merocle/mincab/MinCab_v3.0/Renders/1.png

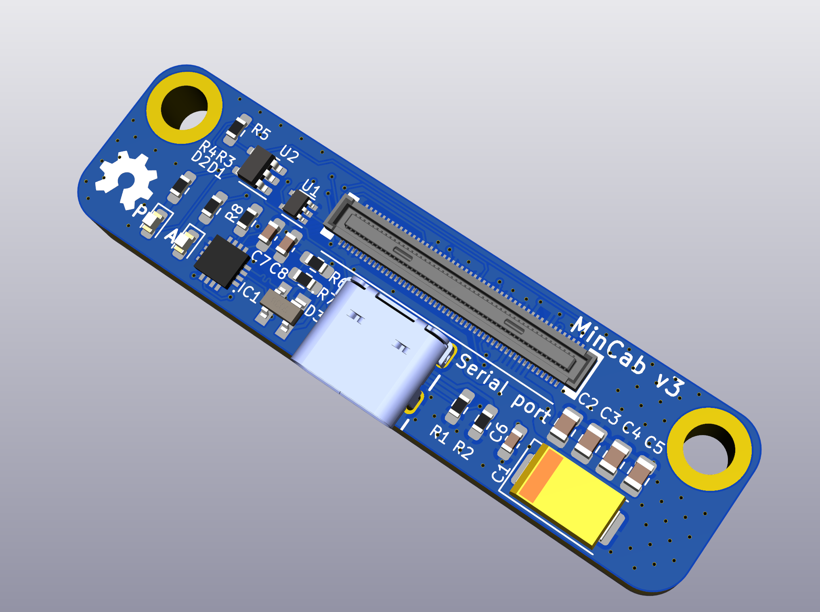
MinCab_v3.0/Renders/1.png
