merocle/mincab/MinCab_v3.0/Renders/2.png

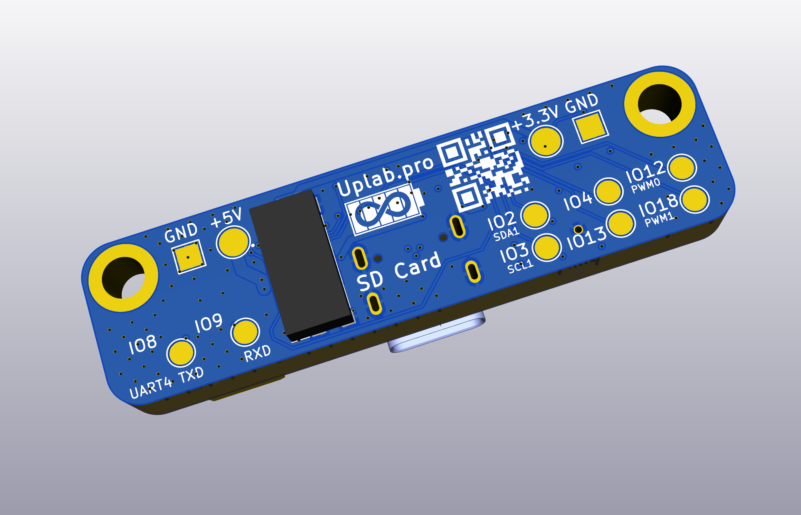
MinCab_v3.0/Renders/2.png
