merocle/mincab/Photos/1.jpg

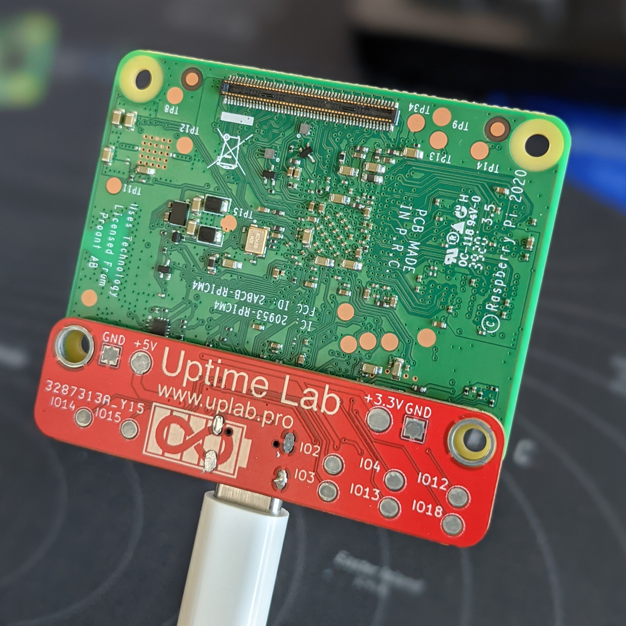
Photos/1.jpg
