merocle/mincab/Photos/2.jpg

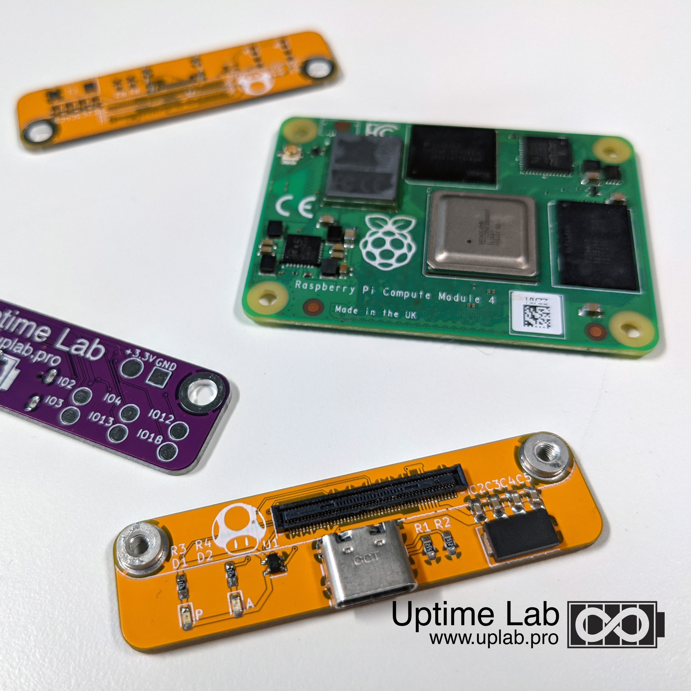
Photos/2.jpg
