merocle/mincab/Photos/3.jpg

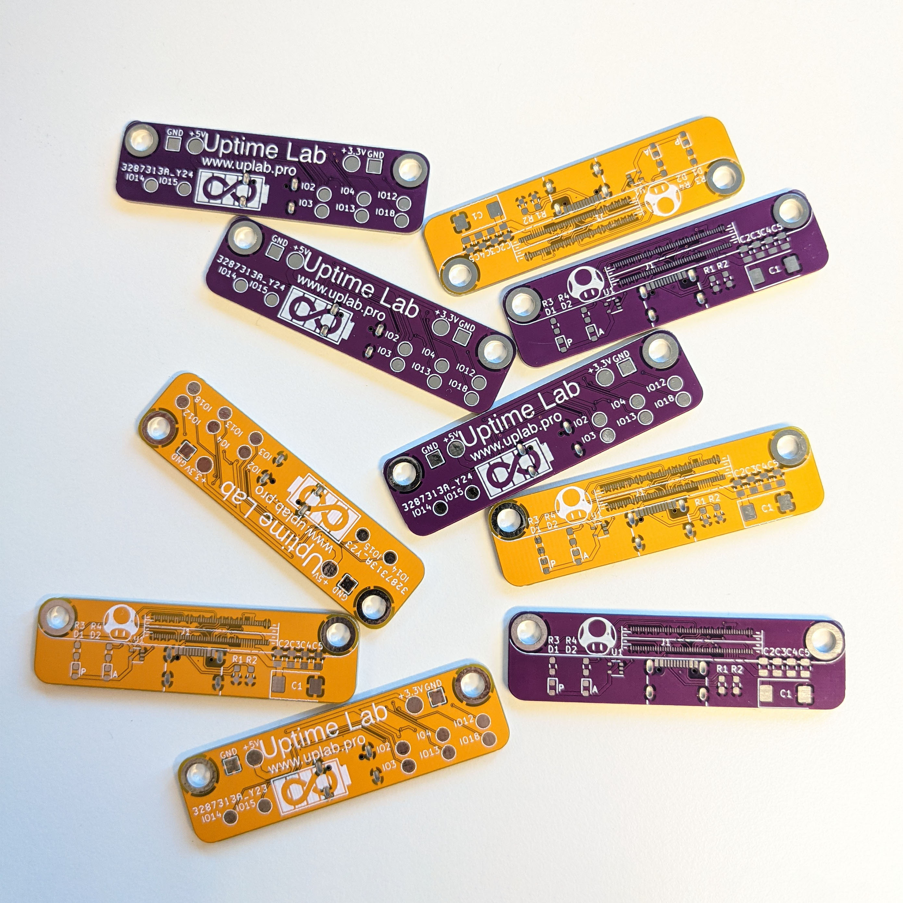
Photos/3.jpg
