merocle/mincab/Photos/4.jpg

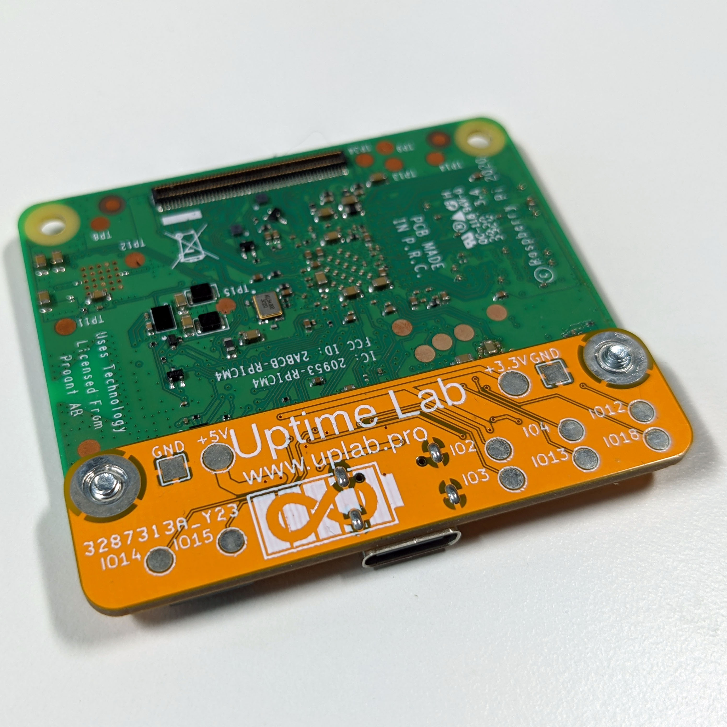
Photos/4.jpg
