merocle/mincab/Photos/5.jpg

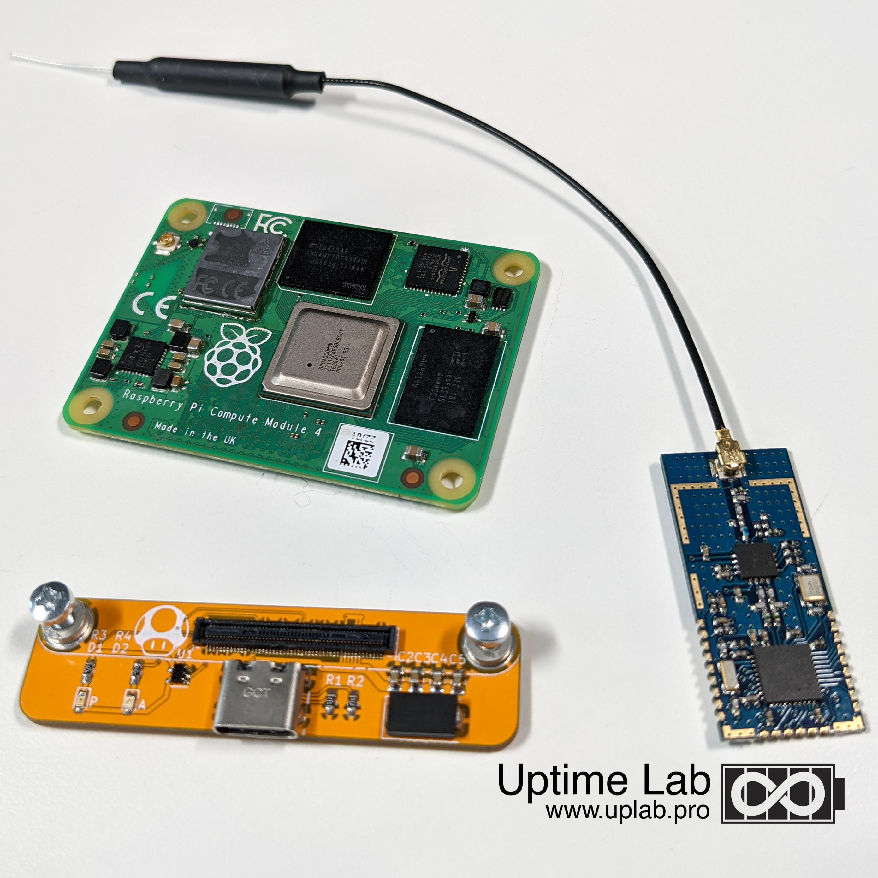
Photos/5.jpg
