merocle/mincab/Photos/6.jpg

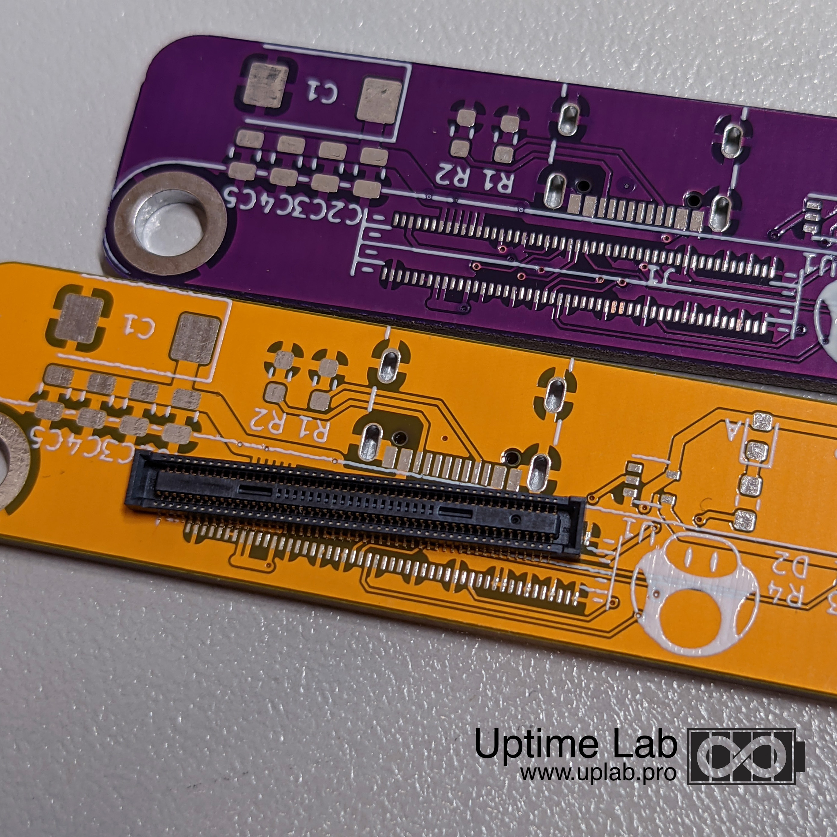
Photos/6.jpg
