merocle/mincab/Photos/7.jpg

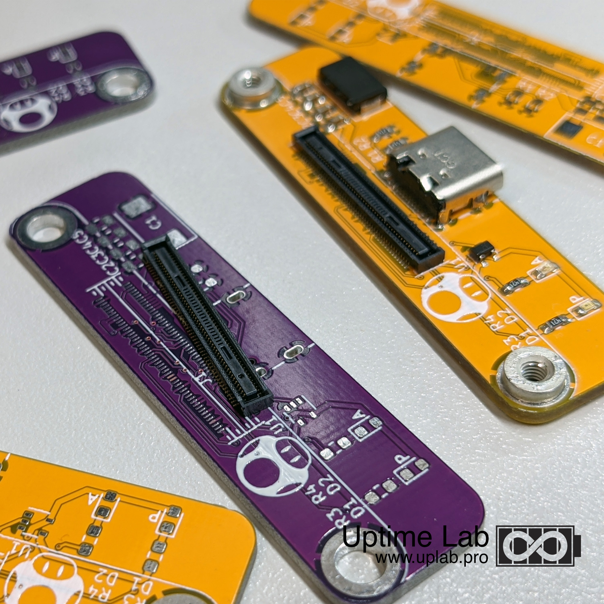
Photos/7.jpg
