merocle/mincab/Photos/8.jpg

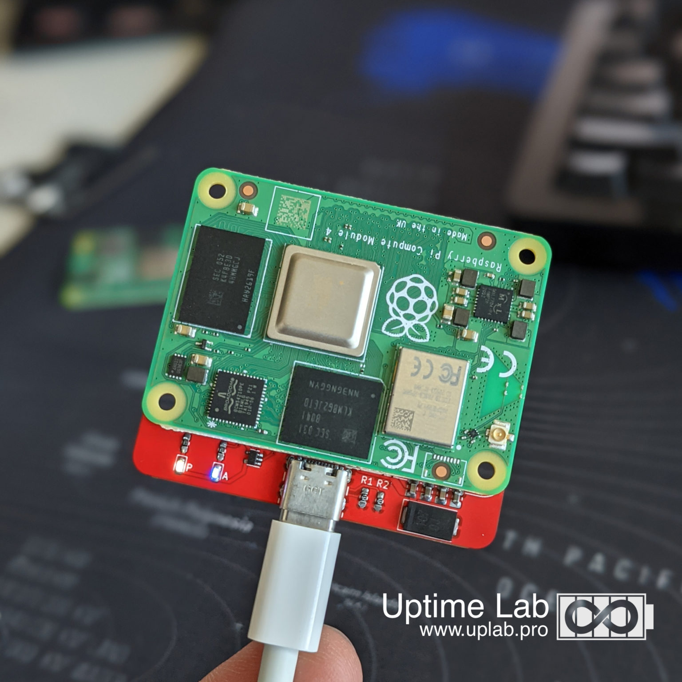
Photos/8.jpg
