merocle/mincab/Photos/9.jpg

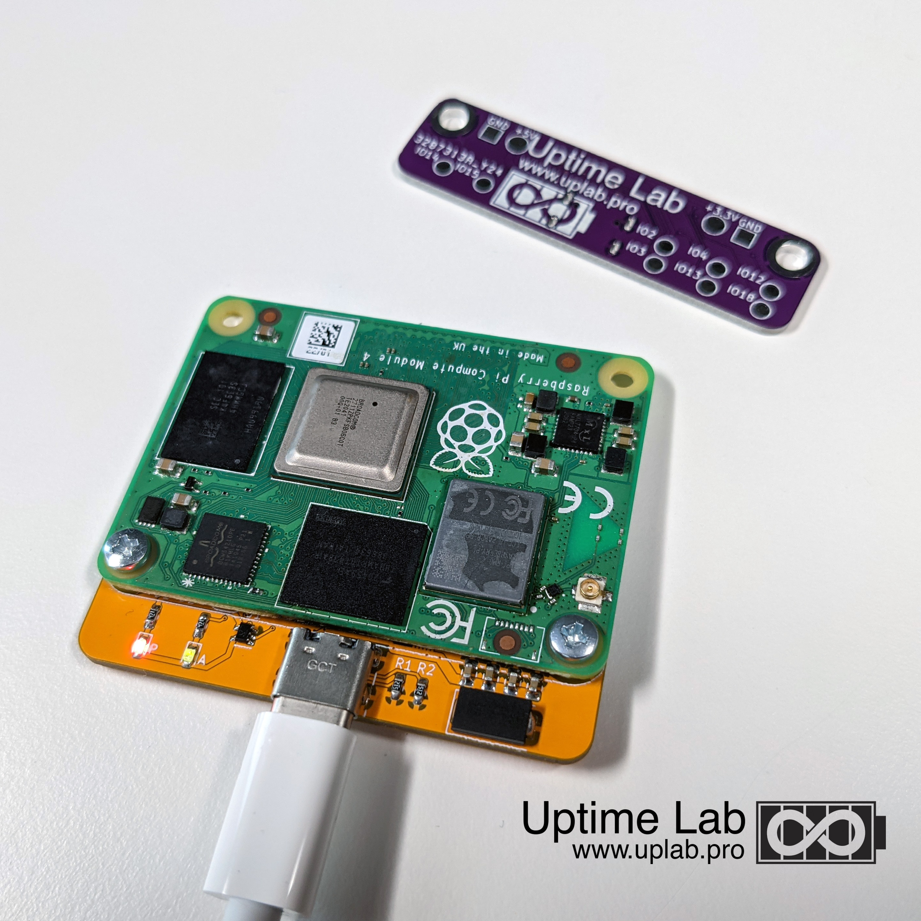
Photos/9.jpg
