merocle/mincab/Photos/10.jpg

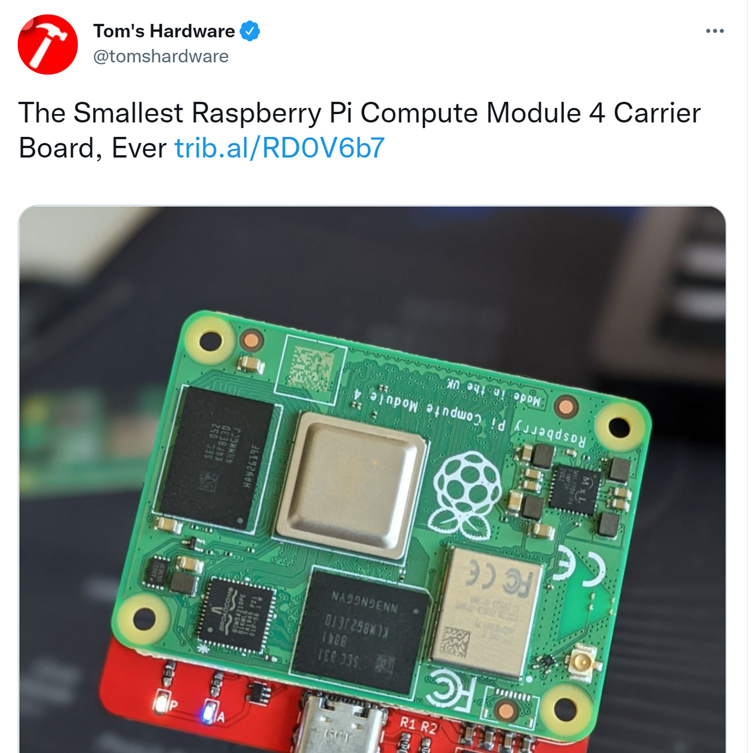
Photos/10.jpg
